yellobyte/DDS-FunctionGenerator-with-AD9833/Doc/Board_V1.0_top.jpg

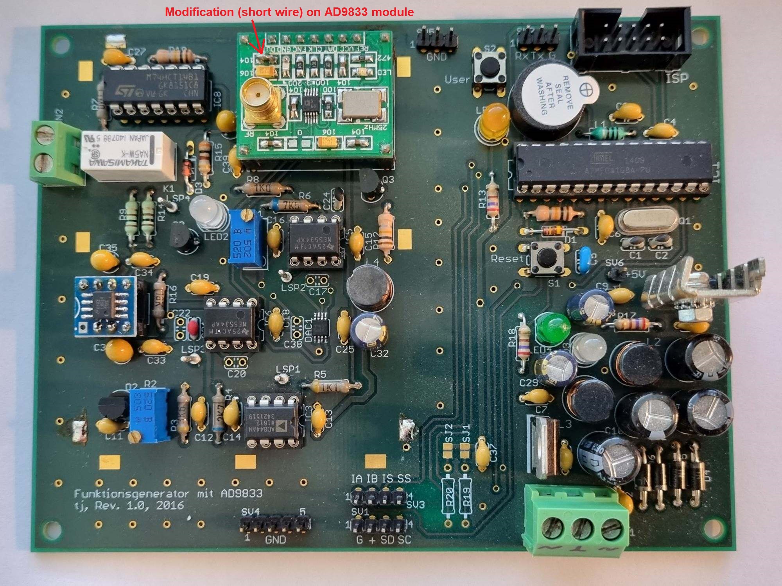
Doc/Board_V1.0_top.jpg
