yellobyte/DDS-FunctionGenerator-with-AD9833/Doc/FrontDisplay-Vpp.jpg

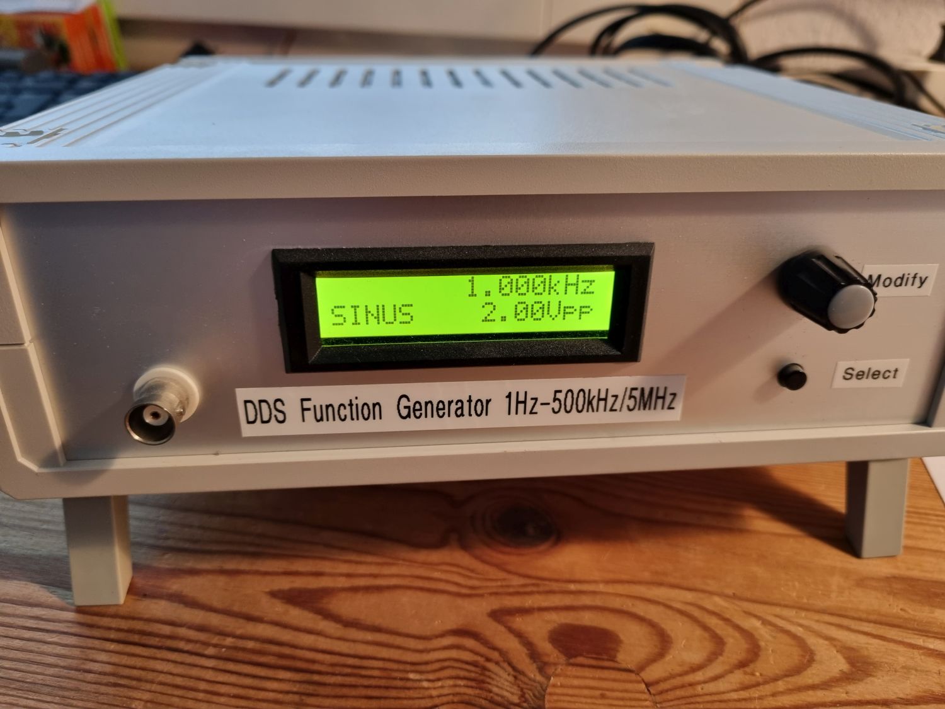
Doc/FrontDisplay-Vpp.jpg
