yellobyte/DDS-FunctionGenerator-with-AD9833/EagleFiles/Board_V1.1a.JPG

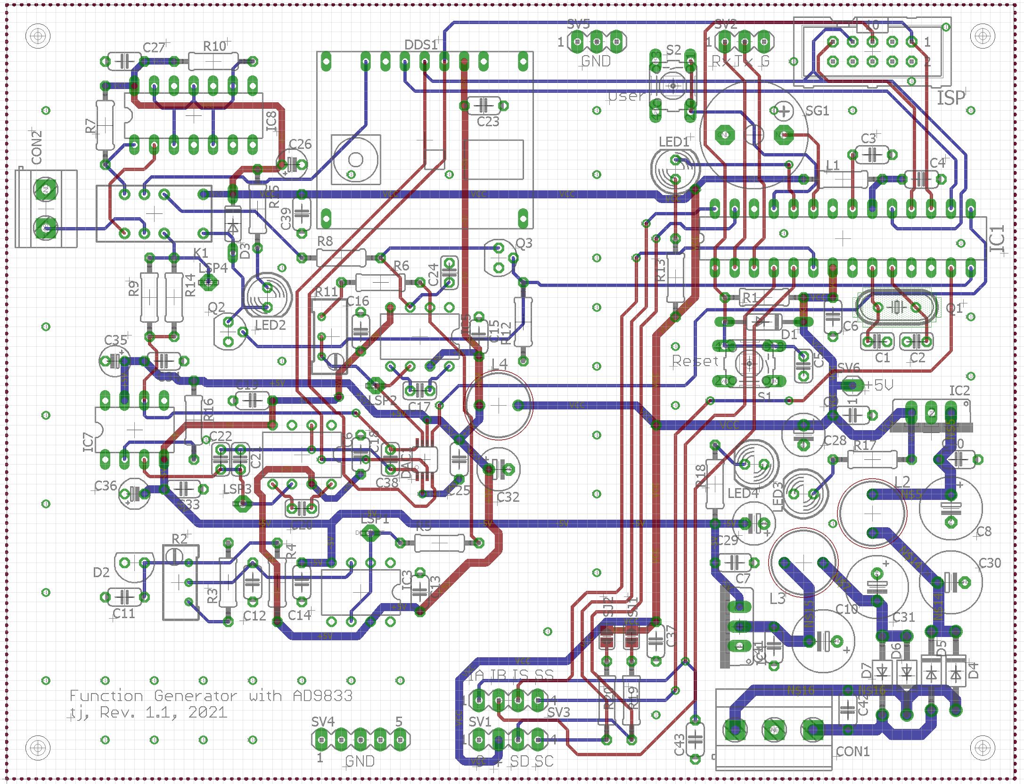
EagleFiles/Board_V1.1a.JPG
