yellobyte/DDS-FunctionGenerator-with-AD9833/EagleFiles/Board_V1.1b.JPG

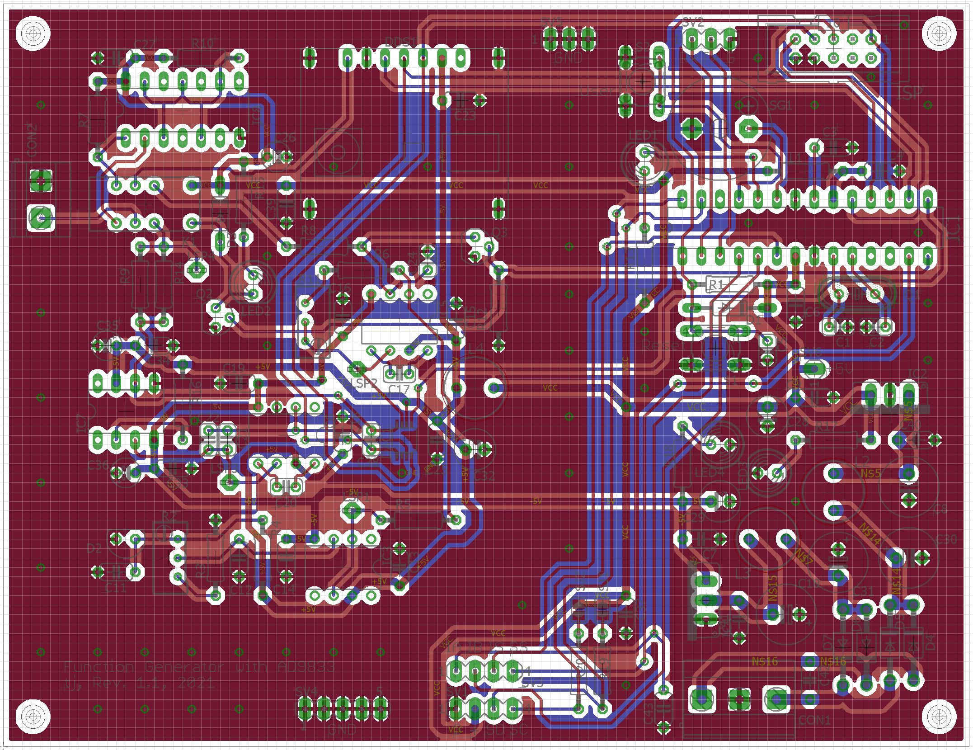
EagleFiles/Board_V1.1b.JPG
